isaacST08/IoT_Window/code/src/opts.h

#ifndef IOT_WINDOW_OPTS_H
#define IOT_WINDOW_OPTS_H
#include "common.h"
#include "pins.h"

// #define OPEN_POSITION_MM 0
// #define CLOSED_POSITION_MM 100

#define WINDOW_WIDTH_MM 200

#define INVERT_DIRECTION 0
#define INVERT_DISPLAY_DIRECTION 0

#define CLOSED_SIDE RIGHT_SIDE

// Which limit switch is on which side.
#define LS_LEFT LS_1
#define LS_RIGHT LS_2

// Which side to home to.
#define HOME_SIDE RIGHT_SIDE

// **==============================================**
// ||          <<<<< BASIC OPTIONS >>>>>           ||
// **==============================================**

// #define SM_FULL_STEPS_PER_REV 200
// #define SM_FULL_STEPS_PER_MM 100
//
// #define LEFT 1
// #define RIGHT 0
//
// #define SM_OPEN 0
// #define SM_CLOSE 100 * SM_FULL_STEPS_PER_MM + SM_OPEN  // 10cm

// **=================================================**
// ||          <<<<< ADVANCED OPTIONS >>>>>           ||
// **=================================================**

// #define SM_FULL_STEPS_PER_REV 200
// #define SM_FULL_STEPS_PER_MM 100

#endif
